phanben110/Robot-Omni-3-wheels-RTOS/3DSimulation/OMNI-cọc đồng/cọc đồng 6mm/M3 x 6mm A-F x 25mm Hexagon Male-Female Threaded Pillar.jpg

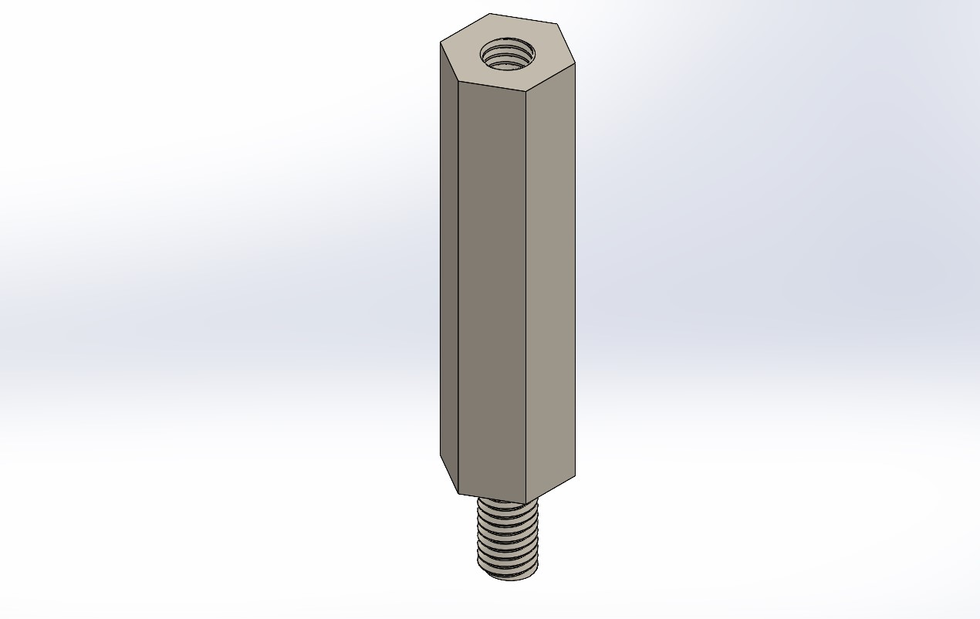
3DSimulation/OMNI-cọc đồng/cọc đồng 6mm/M3 x 6mm A-F x 25mm Hexagon Male-Female Threaded Pillar.jpg
