phanben110/Robot-Omni-3-wheels-RTOS/3DSimulation/OMNI-DRIVER/2016-12-01_19-26-19.png

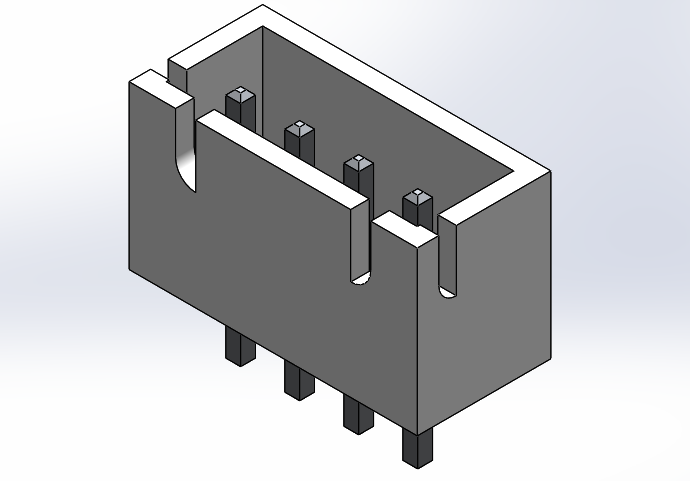
3DSimulation/OMNI-DRIVER/2016-12-01_19-26-19.png
