phanben110/Robot-Omni-3-wheels-RTOS/3DSimulation/OMNI-DRIVER/Cytron 30A Driver2.JPG

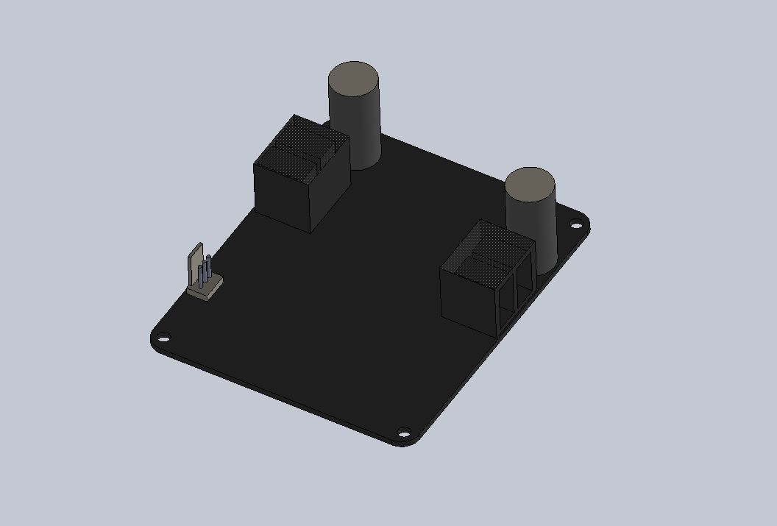
3DSimulation/OMNI-DRIVER/Cytron 30A Driver2.JPG
