phanben110/Robot-Omni-3-wheels-RTOS/3DSimulation/OMNI-DRIVER/Renderings/render.png

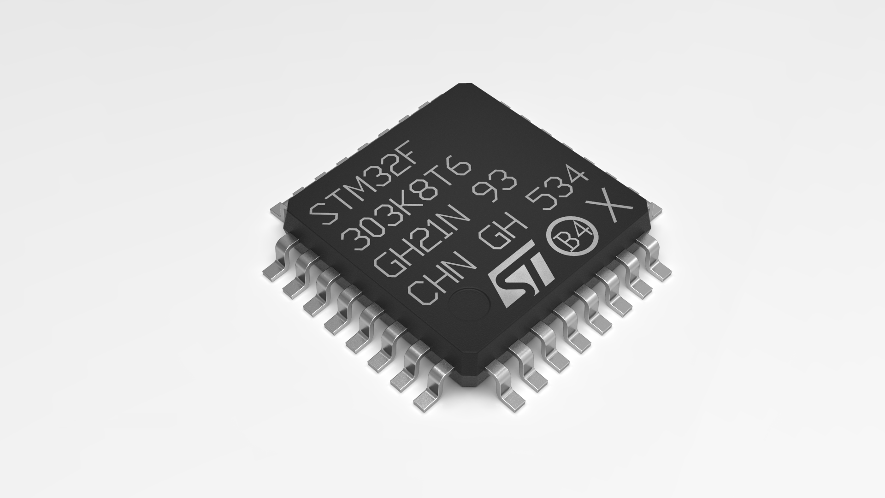
3DSimulation/OMNI-DRIVER/Renderings/render.png
