phanben110/Robot-Omni-3-wheels-RTOS/3DSimulation/OMNI-GÁ ĐỘNG CƠ/Screenshot (53).png

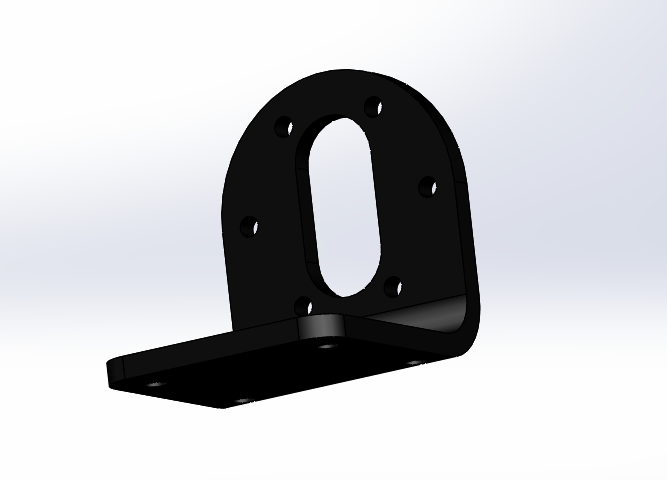
3DSimulation/OMNI-GÁ ĐỘNG CƠ/Screenshot (53).png
