phanben110/Robot-Omni-3-wheels-RTOS/3DSimulation/OMNI-ĐỘNG CƠ/JGB37-520.JPG

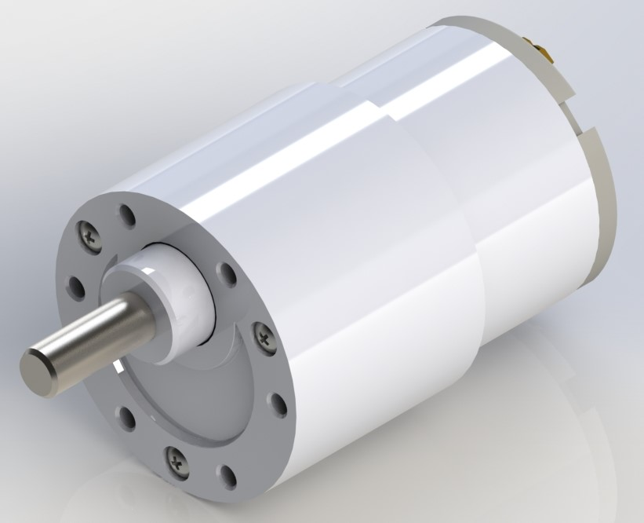
3DSimulation/OMNI-ĐỘNG CƠ/JGB37-520.JPG
