phanben110/Robot-Omni-3-wheels-RTOS/3DSimulation/OMNI-LIDAR/6.Lidar.SLDPRT

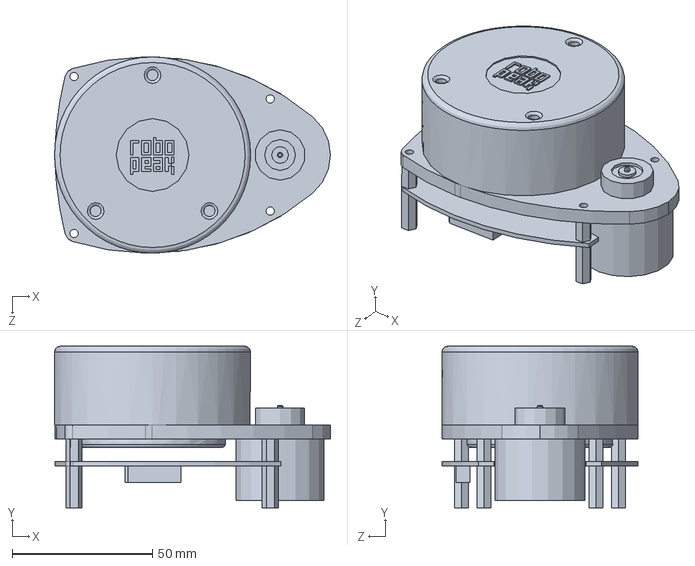
[picture p29: CAD file, 2022-06-20]
3DSimulation/OMNI-LIDAR/6.Lidar.SLDPRT
98.5 x 57.7 x 70.0 mm
