phanben110/Robot-Omni-3-wheels-RTOS/3DSimulation/OMNI-pin lipo/lipo-8-5-3cm.SLDPRT

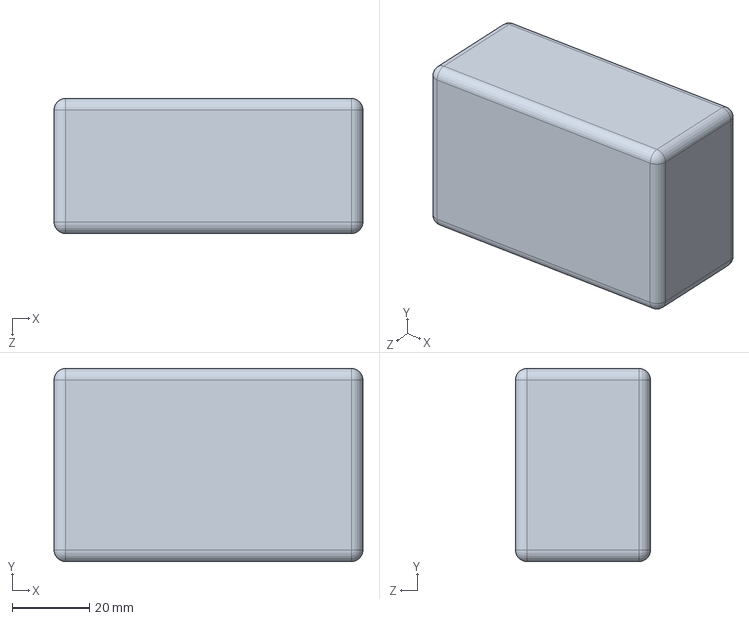
[picture p30: CAD file, 2022-06-20]
3DSimulation/OMNI-pin lipo/lipo-8-5-3cm.SLDPRT
80.0 x 50.0 x 35.0 mm
