phanben110/Robot-Omni-3-wheels-RTOS/3DSimulation/OMNI-raspberry 4/raspberry pi 4/Raspberry Pi 4 B.STEP

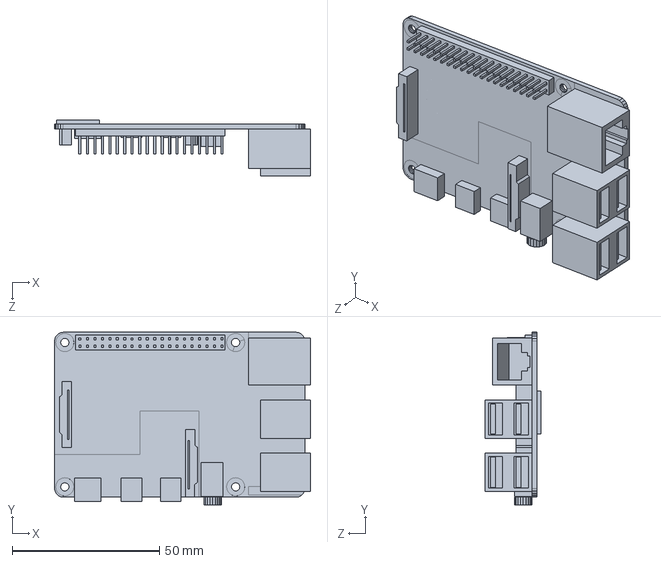
[picture p31: CAD file, 2022-06-20]
3DSimulation/OMNI-raspberry 4/raspberry pi 4/Raspberry Pi 4 B.STEP
86.9 x 58.6 x 19.0 mm
