phanben110/Robot-Omni-3-wheels-RTOS/3DSimulation/OMNI-ĐỘNG CƠ/diaencoder.SLDPRT

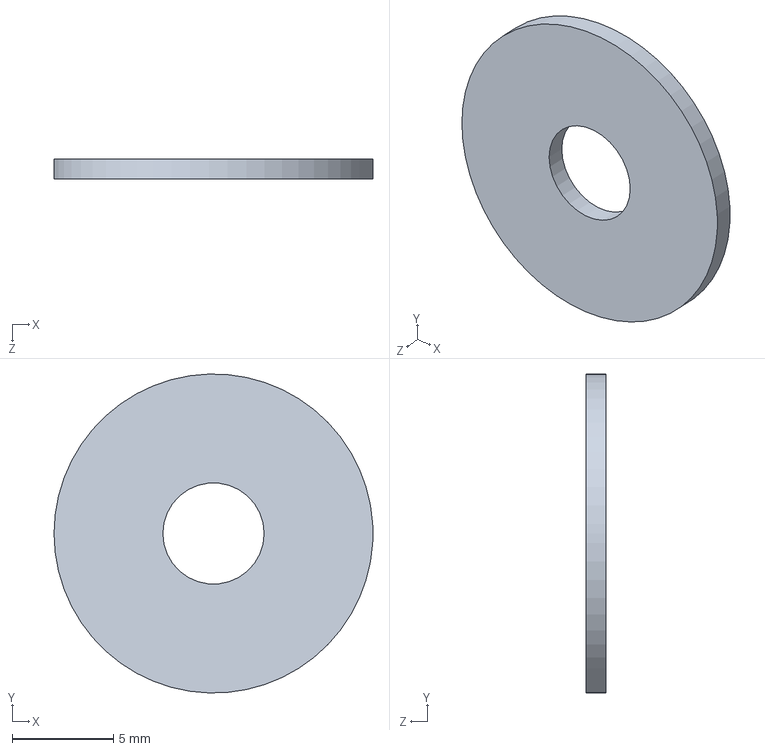
[picture p32: CAD file, 2022-06-20]
3DSimulation/OMNI-ĐỘNG CƠ/diaencoder.SLDPRT
15.8 x 15.7 x 1.00 mm
