phanben110/Robot-Omni-3-wheels-RTOS/3DSimulation/thành sân h=10cm.SLDPRT

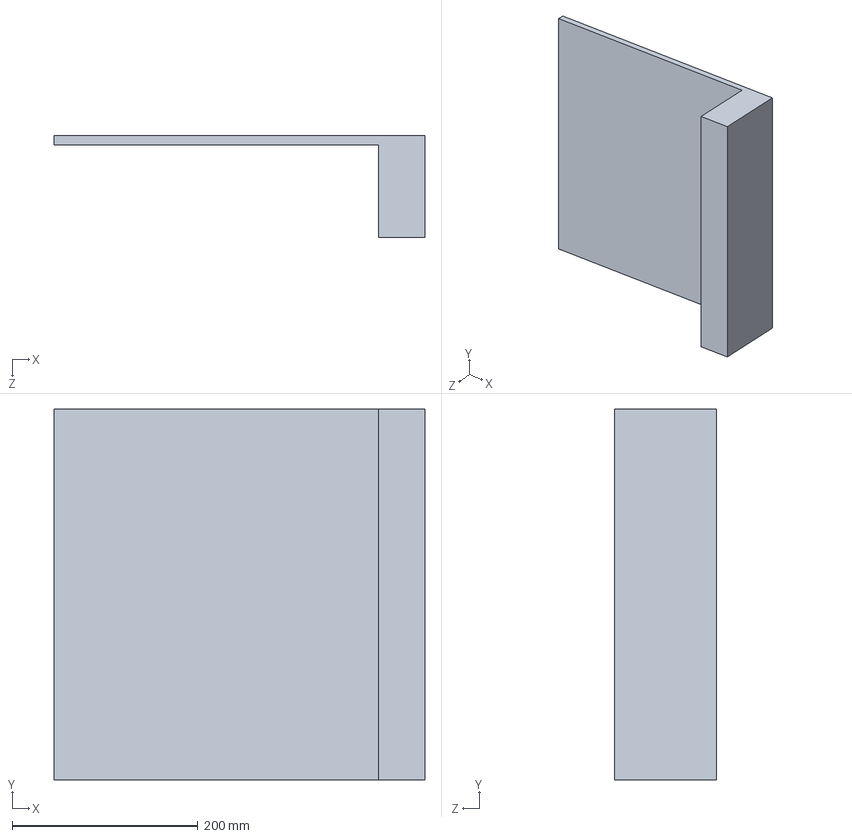
[picture p33: CAD file, 2022-06-20]
3DSimulation/thành sân h=10cm.SLDPRT
400.0 x 400.0 x 110.0 mm
