phanben110/Robot-Omni-3-wheels-RTOS/3DSimulation/file cắt cnc/VERSION 2.95 (main)/khung robot ver 2.95 mat duoi inox 3li.DXF

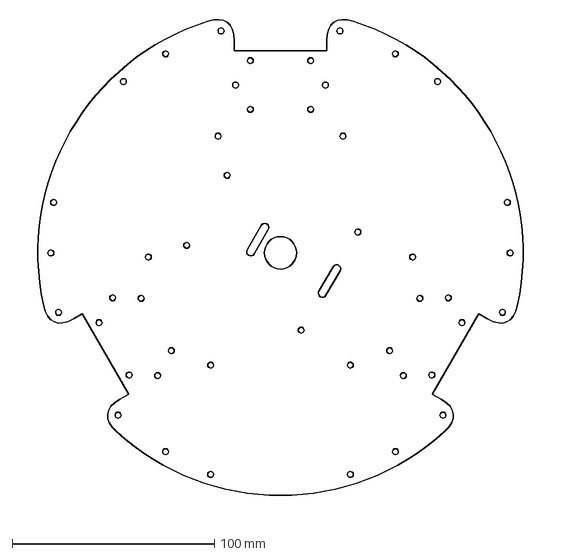
[picture p34: CAD file, 2022-06-20]
3DSimulation/file cắt cnc/VERSION 2.95 (main)/khung robot ver 2.95 mat duoi inox 3li.DXF
261.5 x 247.6 mm
