phanben110/Robot-Omni-3-wheels-RTOS/3DSimulation/file cắt cnc/VERSION 3.2/khung robot ver 3.2 mat duoi.DXF

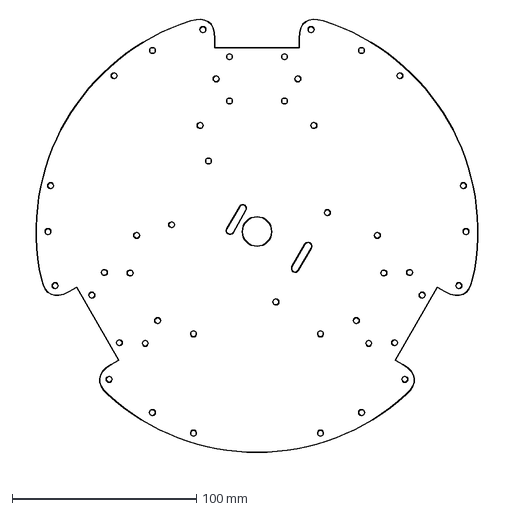
[picture p35: CAD file, 2022-06-20]
3DSimulation/file cắt cnc/VERSION 3.2/khung robot ver 3.2 mat duoi.DXF
261.5 x 247.6 mm
