phanben110/Robot-Omni-3-wheels-RTOS/3DSimulation/OMNI-BÁNH NHÔM 60mm/Wheel/Wheel - Rubber-8.STL

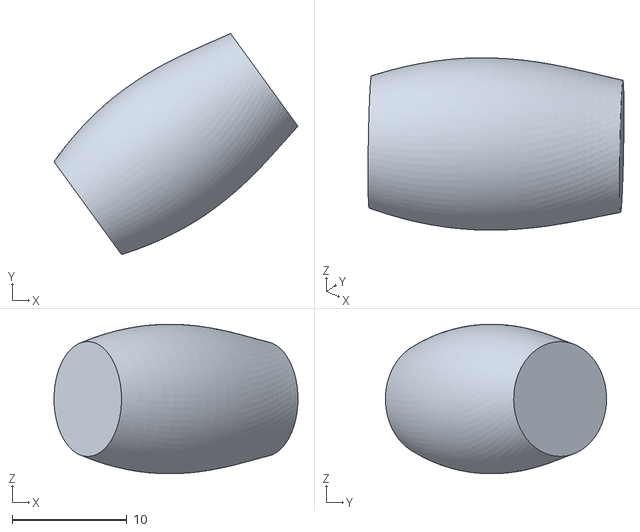
[picture p36: CAD file, 2022-06-20]
3DSimulation/OMNI-BÁNH NHÔM 60mm/Wheel/Wheel - Rubber-8.STL
21.2 x 19.3 x 13.0
