phanben110/Robot-Omni-3-wheels-RTOS/3DSimulation/OMNI-DRIVER/ırlz44nstep.STEP

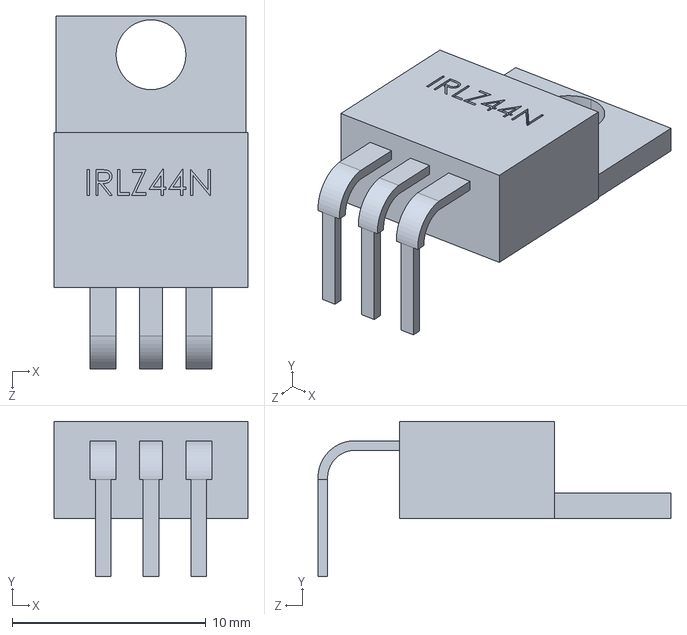
[picture p37: CAD file, 2022-06-20]
3DSimulation/OMNI-DRIVER/ırlz44nstep.STEP
10.0 x 8.00 x 18.2 mm
