phanben110/Robot-Omni-3-wheels-RTOS/3DSimulation/OMNI-encoder/38 mm OD, 6 mm Shaft, Incremental Optical Rotary Encoder.STEP

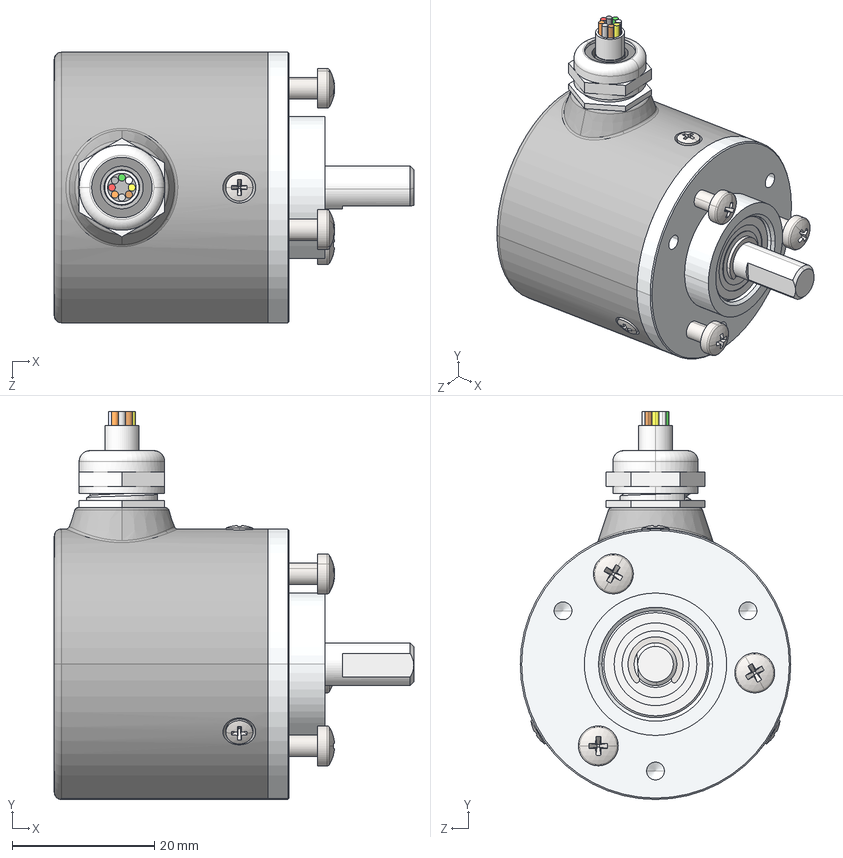
[picture p38: CAD file, 2022-06-20]
3DSimulation/OMNI-encoder/38 mm OD, 6 mm Shaft, Incremental Optical Rotary Encoder.STEP
50.5 x 54.5 x 38.0 mm
Encasing, 38 mm OD, 6 mm Shaft, Incremental Optical Rotary Encoder
Shaft Holding Body, 38 mm OD, 6 mm Shaft, Incremental Optical Rotary Encoder
696Z Ball Bearing, 38 mm OD, 6 mm Shaft, Incremental Optical Rotary Encoder_default
Shaft, 38 mm OD, 6 mm Shaft, Incremental Optical Rotary Encoder
Grommet, 38 mm OD, 6 mm Shaft, Incremental Optical Rotary Encoder
Cable Gland Coupling Nut, 38 mm OD, 6 mm Shaft, Incremental Optical Rotary Encoder
Cable Gland Coupling Fastening Nut, 38 mm OD, 6 mm Shaft, Incremental Optical Rotary Encoder
Cable, 38 mm OD, 6 mm Shaft, Incremental Optical Rotary Encoder
oval head_am_B18.6.7M - M2 x 0.4 x 4 Type I Cross Recessed OHMS --4N x 3
c-ring external retaining ring_am_B27.8M - 3FM1-6
pan cross head_am_B18.6.7M - M3 x 0.5 x 8 Type I Cross Recessed PHMS --8N x 3
