phanben110/Robot-Omni-3-wheels-RTOS/3DSimulation/OMNI-KHUNG ROBOT/thanh bắt chéo cố định 2 chân động cơ.SLDPRT

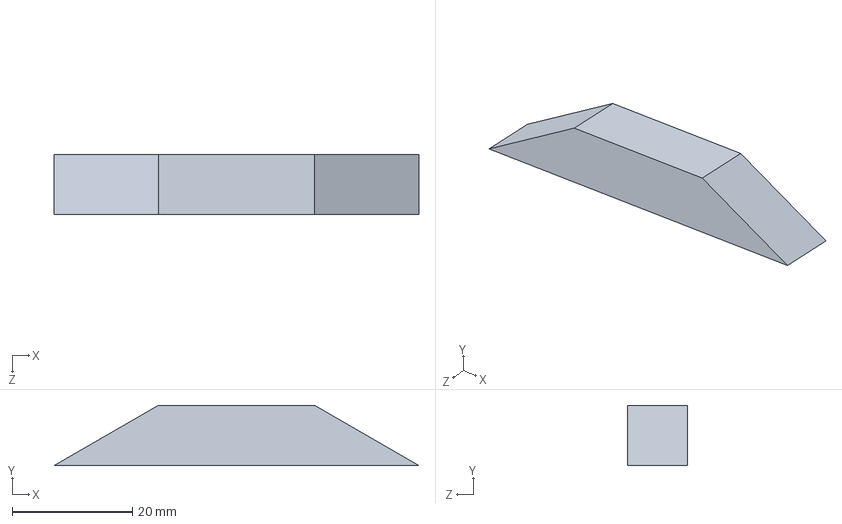
[picture p39: CAD file, 2022-06-20]
3DSimulation/OMNI-KHUNG ROBOT/thanh bắt chéo cố định 2 chân động cơ.SLDPRT
60.6 x 10.0 x 10.0 mm
