phanben110/Robot-Omni-3-wheels-RTOS/3DSimulation/OMNI-ĐỘNG CƠ/GEARED BODY, MOTOR, JGB37-520.SLDPRT

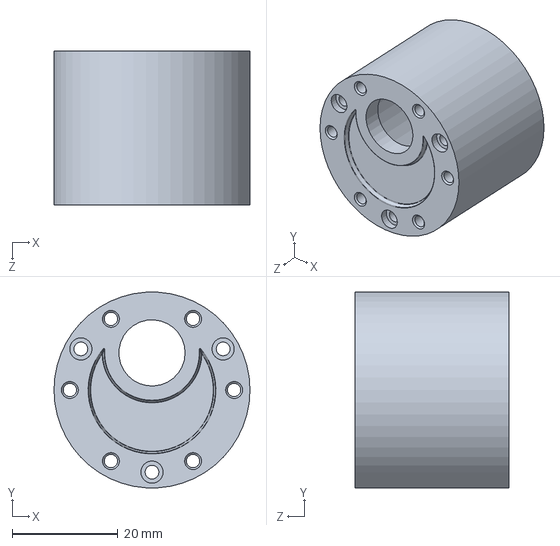
[picture p40: CAD file, 2022-06-20]
3DSimulation/OMNI-ĐỘNG CƠ/GEARED BODY, MOTOR, JGB37-520.SLDPRT
37.0 x 36.9 x 29.0 mm
