phanben110/Robot-Omni-3-wheels-RTOS/3DSimulation/OMNI-BÁNH NHÔM 60mm/Wheel/Wheel - Rubber-10.STL

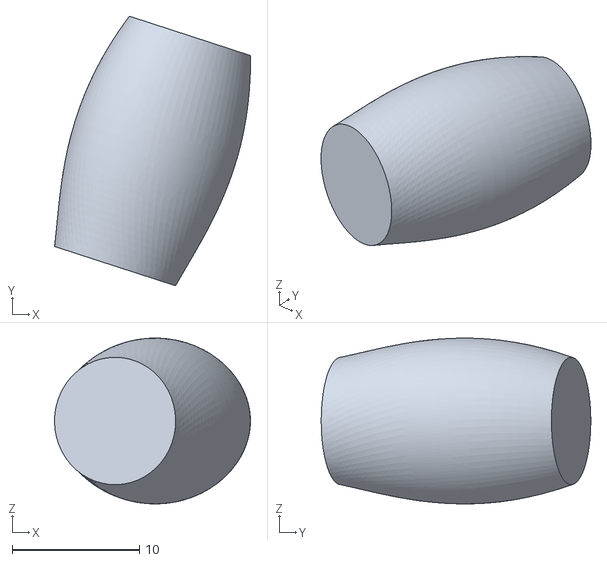
[picture p41: CAD file, 2022-06-20]
3DSimulation/OMNI-BÁNH NHÔM 60mm/Wheel/Wheel - Rubber-10.STL
15.4 x 21.2 x 13.0
