phanben110/Robot-Omni-3-wheels-RTOS/3DSimulation/OMNI-KHUNG ROBOT/file test M3.SLDPRT

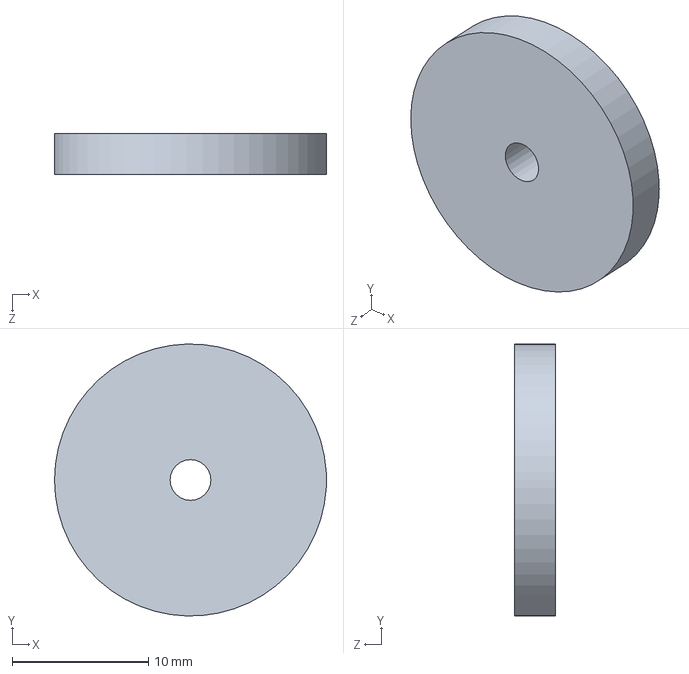
[picture p43: CAD file, 2022-06-20]
3DSimulation/OMNI-KHUNG ROBOT/file test M3.SLDPRT
20.0 x 20.0 x 3.00 mm
