phanben110/Robot-Omni-3-wheels-RTOS/3DSimulation/OMNI-ĐỘNG CƠ/PLASTIC COVER, DC MOTOR, JGB37-520.SLDPRT

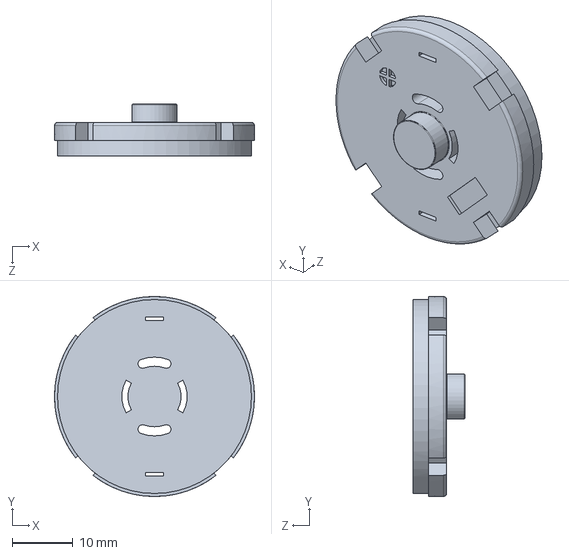
[picture p44: CAD file, 2022-06-20]
3DSimulation/OMNI-ĐỘNG CƠ/PLASTIC COVER, DC MOTOR, JGB37-520.SLDPRT
33.0 x 33.0 x 8.50 mm
