phanben110/Robot-Omni-3-wheels-RTOS/3DSimulation/OMNI-encoder/Shaft, 38 mm OD, 6 mm Shaft, Incremental Optical Rotary Encoder.SLDPRT

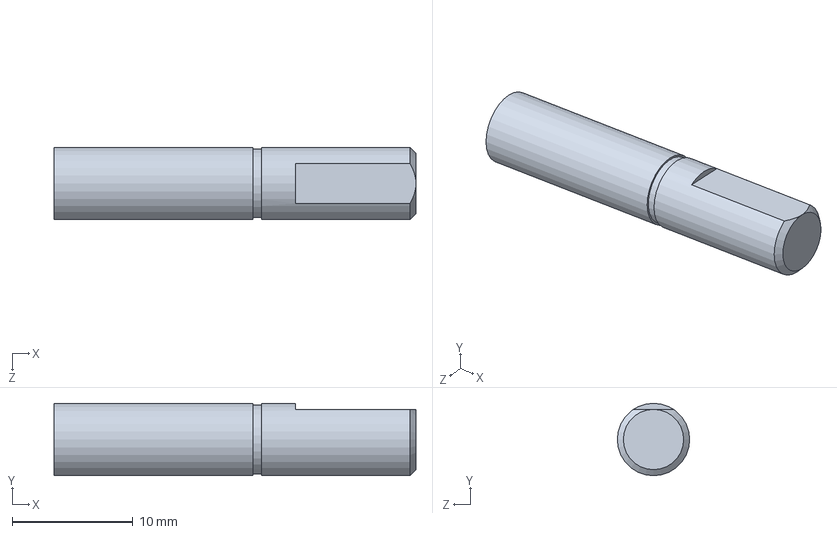
[picture p45: CAD file, 2022-06-20]
3DSimulation/OMNI-encoder/Shaft, 38 mm OD, 6 mm Shaft, Incremental Optical Rotary Encoder.SLDPRT
30.0 x 6.00 x 6.00 mm
