phanben110/Robot-Omni-3-wheels-RTOS/3DSimulation/OMNI-KHUNG ROBOT/khung chân của 1 động cơ.SLDPRT

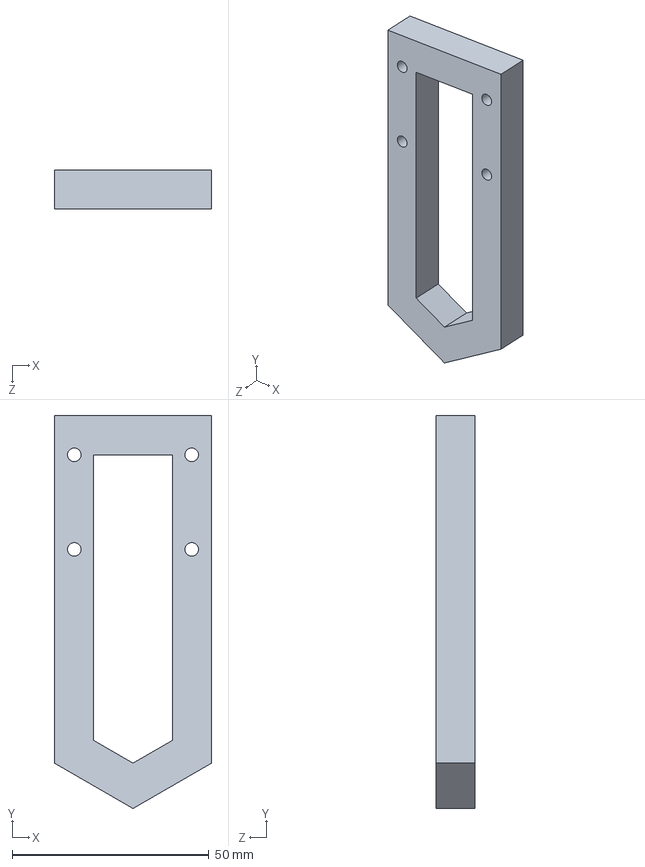
[picture p46: CAD file, 2022-06-20]
3DSimulation/OMNI-KHUNG ROBOT/khung chân của 1 động cơ.SLDPRT
40.0 x 100.0 x 10.0 mm
