phanben110/Robot-Omni-3-wheels-RTOS/3DSimulation/OMNI-ĐỘNG CƠ/COUPLING BRACKET, GEARED BODY TO DC MOTOR, JGB37-520.SLDPRT

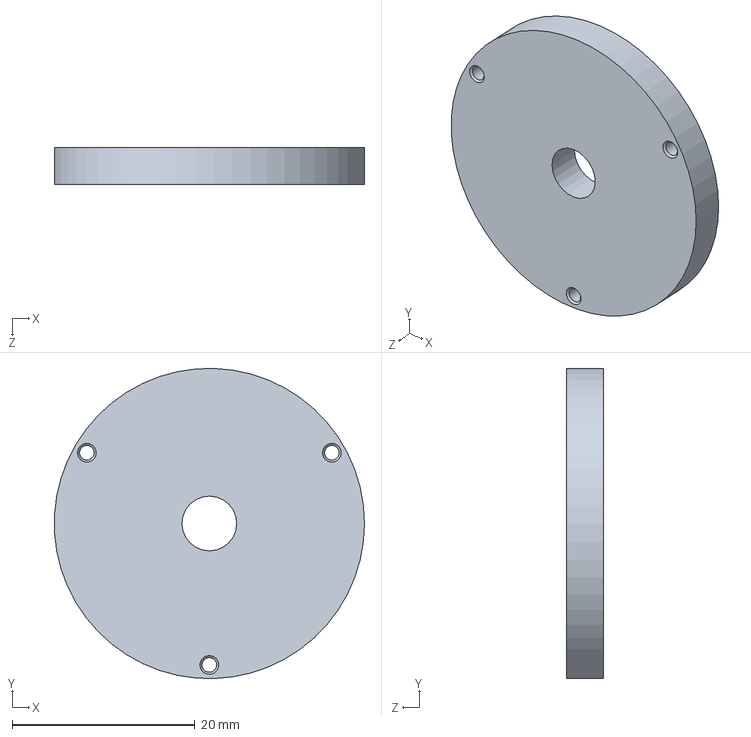
[picture p47: CAD file, 2022-06-20]
3DSimulation/OMNI-ĐỘNG CƠ/COUPLING BRACKET, GEARED BODY TO DC MOTOR, JGB37-520.SLDPRT
34.0 x 34.0 x 4.00 mm
