phanben110/Robot-Omni-3-wheels-RTOS/3DSimulation/OMNI-DRIVER/board driver.SLDPRT

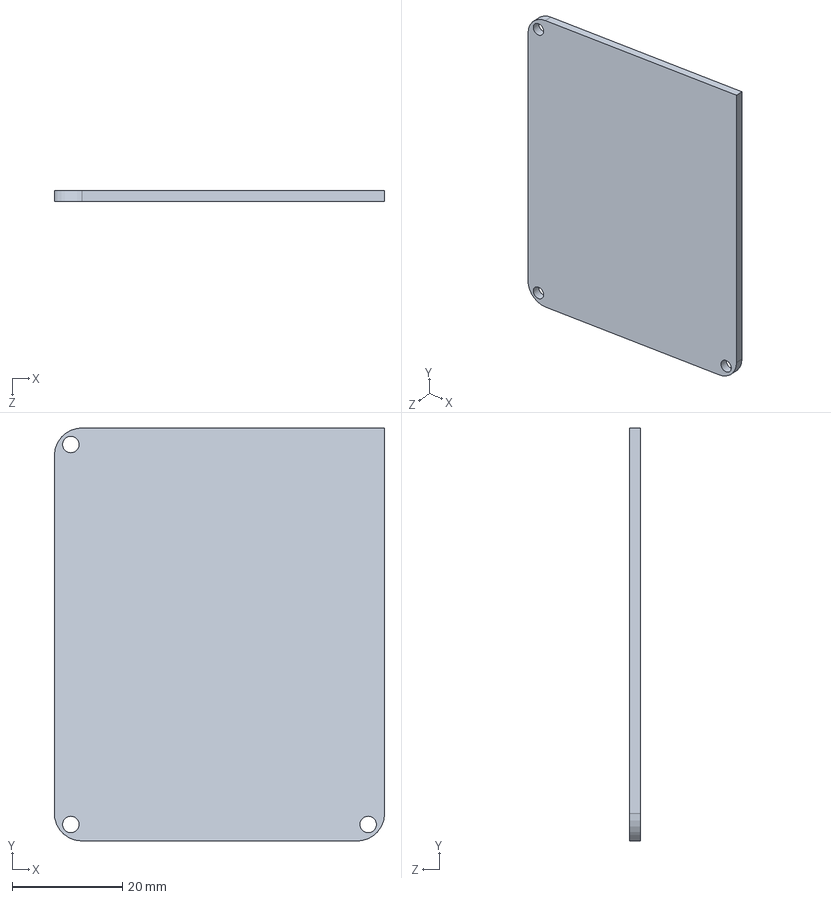
[picture p48: CAD file, 2022-06-20]
3DSimulation/OMNI-DRIVER/board driver.SLDPRT
60.0 x 75.0 x 2.00 mm
