phanben110/Robot-Omni-3-wheels-RTOS/3DSimulation/OMNI-encoder/Cable, 38 mm OD, 6 mm Shaft, Incremental Optical Rotary Encoder.SLDPRT

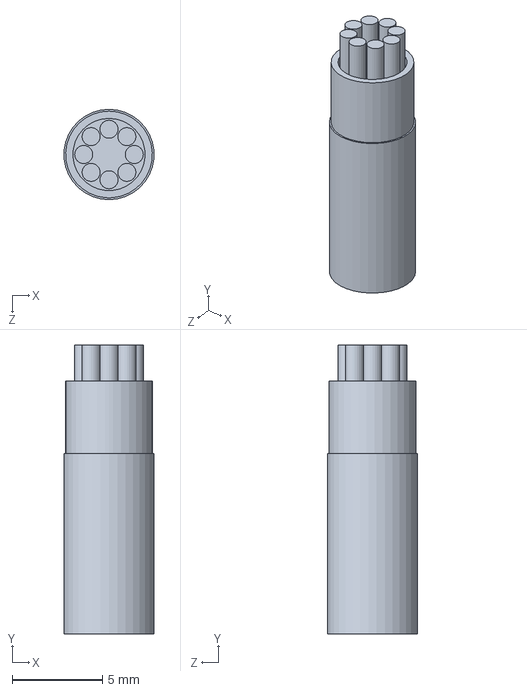
[picture p49: CAD file, 2022-06-20]
3DSimulation/OMNI-encoder/Cable, 38 mm OD, 6 mm Shaft, Incremental Optical Rotary Encoder.SLDPRT
4.98 x 16.0 x 5.00 mm
