phanben110/Robot-Omni-3-wheels-RTOS/3DSimulation/OMNI-KHUNG ROBOT/khung robot cnc.SLDPRT

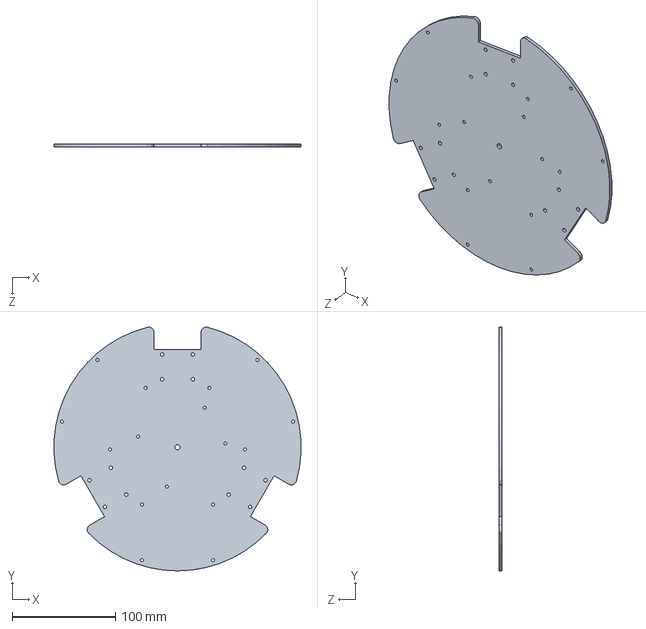
[picture p50: CAD file, 2022-06-20]
3DSimulation/OMNI-KHUNG ROBOT/khung robot cnc.SLDPRT
239.7 x 236.6 x 3.00 mm
