phanben110/Robot-Omni-3-wheels-RTOS/3DSimulation/OMNI-ĐỘNG CƠ/DC MOTOR, JGB37-520.SLDPRT

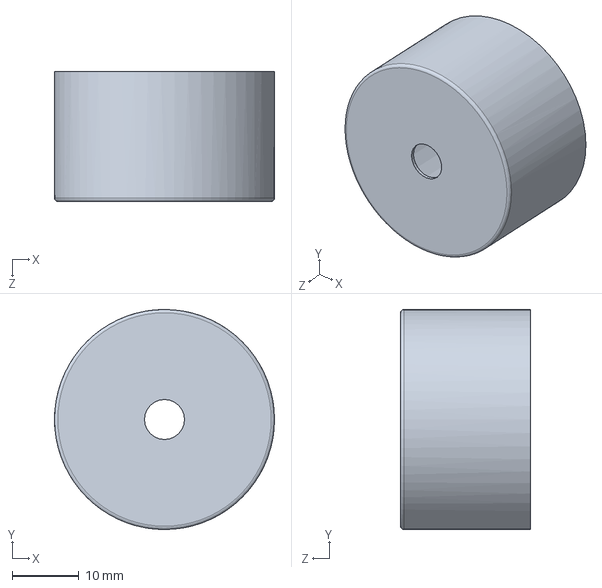
[picture p51: CAD file, 2022-06-20]
3DSimulation/OMNI-ĐỘNG CƠ/DC MOTOR, JGB37-520.SLDPRT
33.0 x 33.0 x 19.5 mm
