phanben110/Robot-Omni-3-wheels-RTOS/3DSimulation/OMNI-BÁNH NHÔM 60mm/Wheel/Wheel - Alu_Base-1.STL

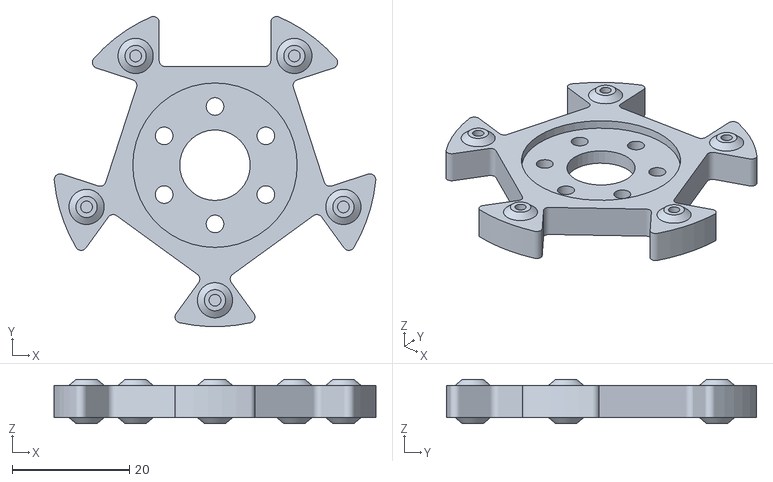
[picture p52: CAD file, 2022-06-20]
3DSimulation/OMNI-BÁNH NHÔM 60mm/Wheel/Wheel - Alu_Base-1.STL
54.8 x 52.8 x 7.50
