phanben110/Robot-Omni-3-wheels-RTOS/3DSimulation/OMNI-encoder/Cable Gland Coupling Fastening Nut, 38 mm OD, 6 mm Shaft, Incremental Optical Rotary Encoder.SLDPRT

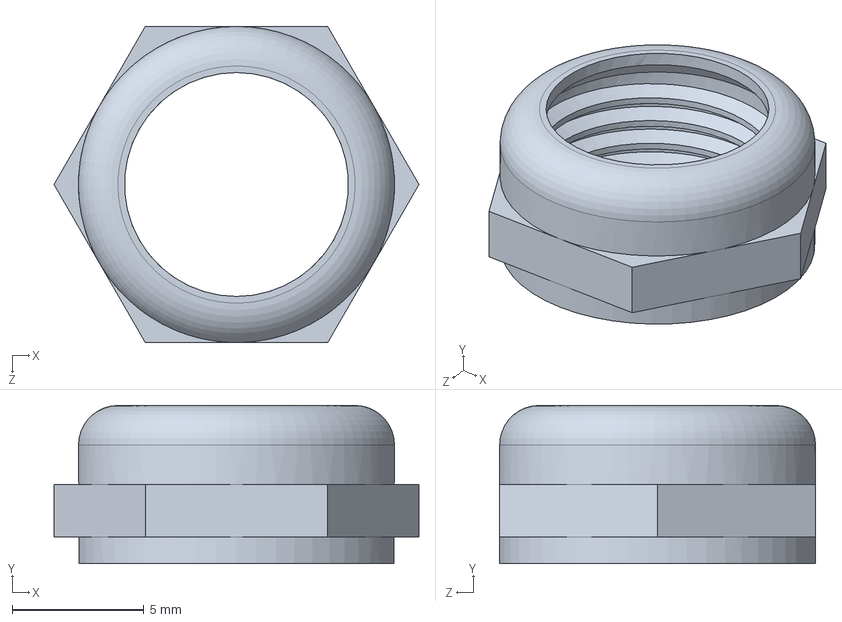
[picture p53: CAD file, 2022-06-20]
3DSimulation/OMNI-encoder/Cable Gland Coupling Fastening Nut, 38 mm OD, 6 mm Shaft, Incremental Optical Rotary Encoder.SLDPRT
13.9 x 6.00 x 12.0 mm
