phanben110/Robot-Omni-3-wheels-RTOS/3DSimulation/OMNI-KHUNG ROBOT/khung robot ver2 mat tren co the chinh sua.SLDPRT

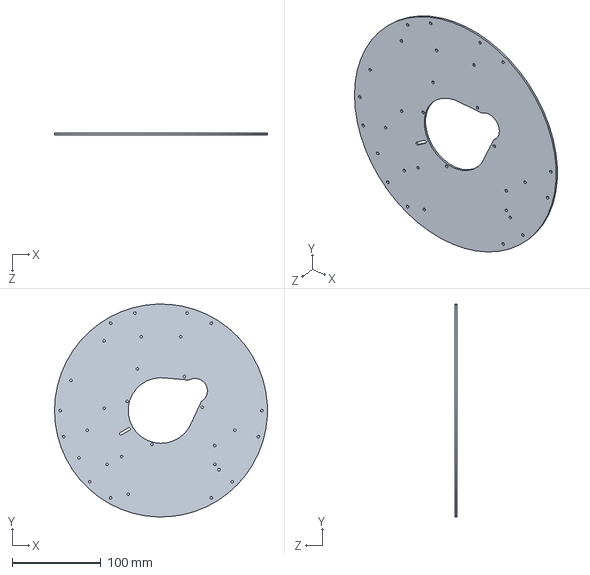
[picture p54: CAD file, 2022-06-20]
3DSimulation/OMNI-KHUNG ROBOT/khung robot ver2 mat tren co the chinh sua.SLDPRT
240.0 x 239.9 x 2.00 mm
