phanben110/Robot-Omni-3-wheels-RTOS/3DSimulation/OMNI-ĐỘNG CƠ/SHAFT COUPLER, JGB37-520.SLDPRT

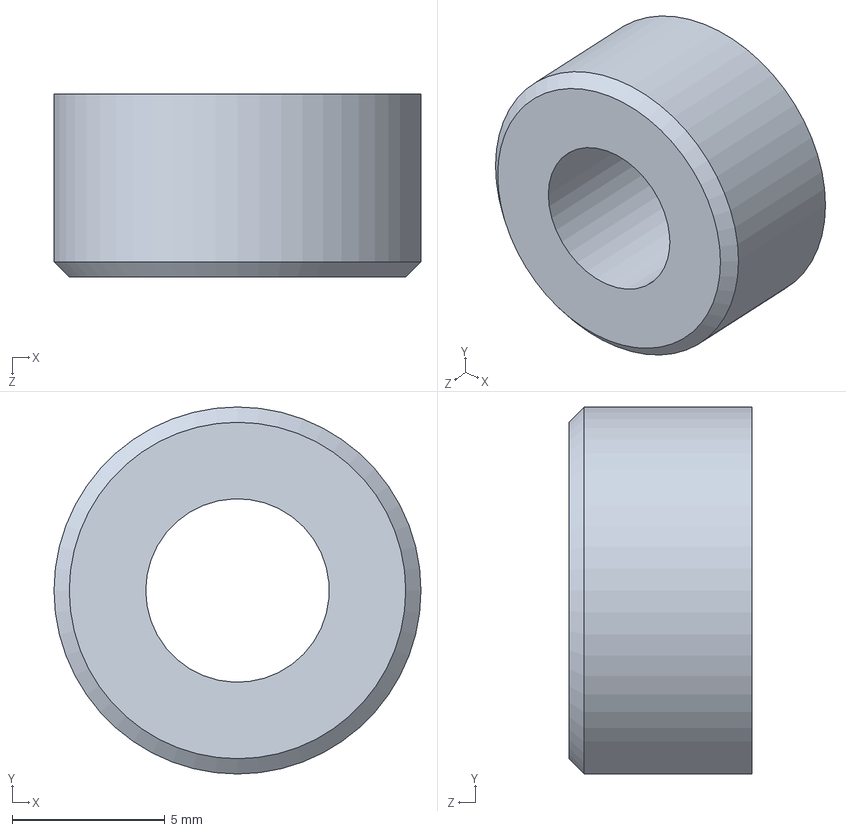
[picture p55: CAD file, 2022-06-20]
3DSimulation/OMNI-ĐỘNG CƠ/SHAFT COUPLER, JGB37-520.SLDPRT
12.0 x 12.0 x 6.00 mm
