phanben110/Robot-Omni-3-wheels-RTOS/3DSimulation/OMNI-encoder/Shaft Holding Body, 38 mm OD, 6 mm Shaft, Incremental Optical Rotary Encoder.SLDPRT

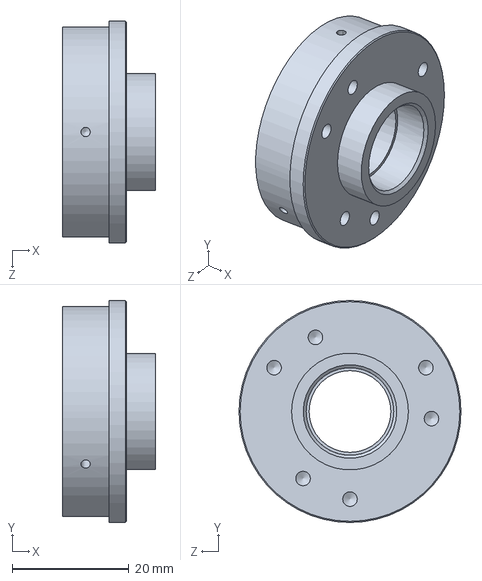
[picture p56: CAD file, 2022-06-20]
3DSimulation/OMNI-encoder/Shaft Holding Body, 38 mm OD, 6 mm Shaft, Incremental Optical Rotary Encoder.SLDPRT
16.0 x 38.0 x 38.0 mm
