phanben110/Robot-Omni-3-wheels-RTOS/3DSimulation/OMNI-KHUNG ROBOT/khung robot cnc mặt trên.SLDPRT

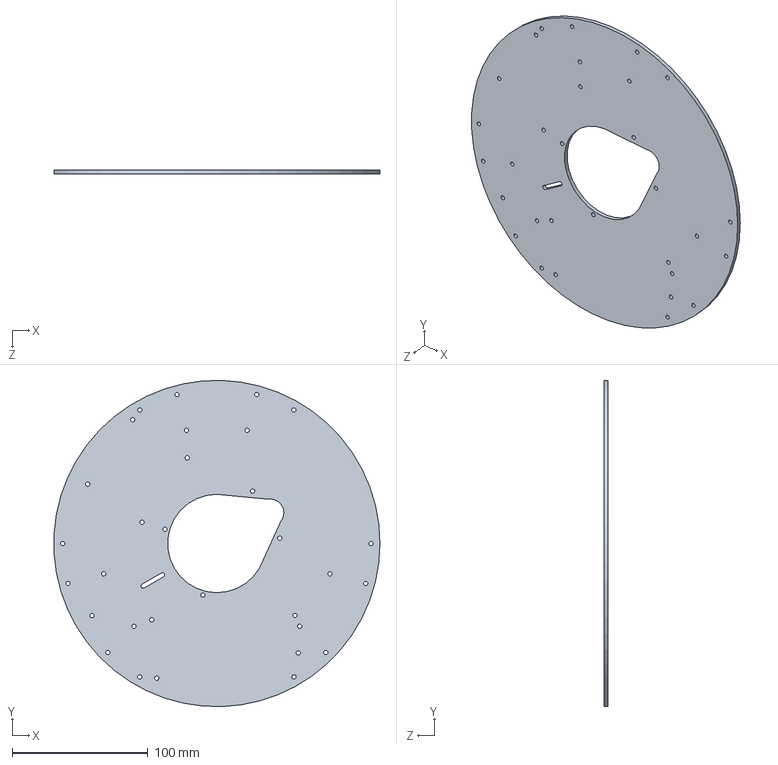
[picture p57: CAD file, 2022-06-20]
3DSimulation/OMNI-KHUNG ROBOT/khung robot cnc mặt trên.SLDPRT
240.3 x 240.4 x 3.00 mm
