phanben110/Robot-Omni-3-wheels-RTOS/3DSimulation/OMNI-ĐỘNG CƠ/JGB37-520.STEP

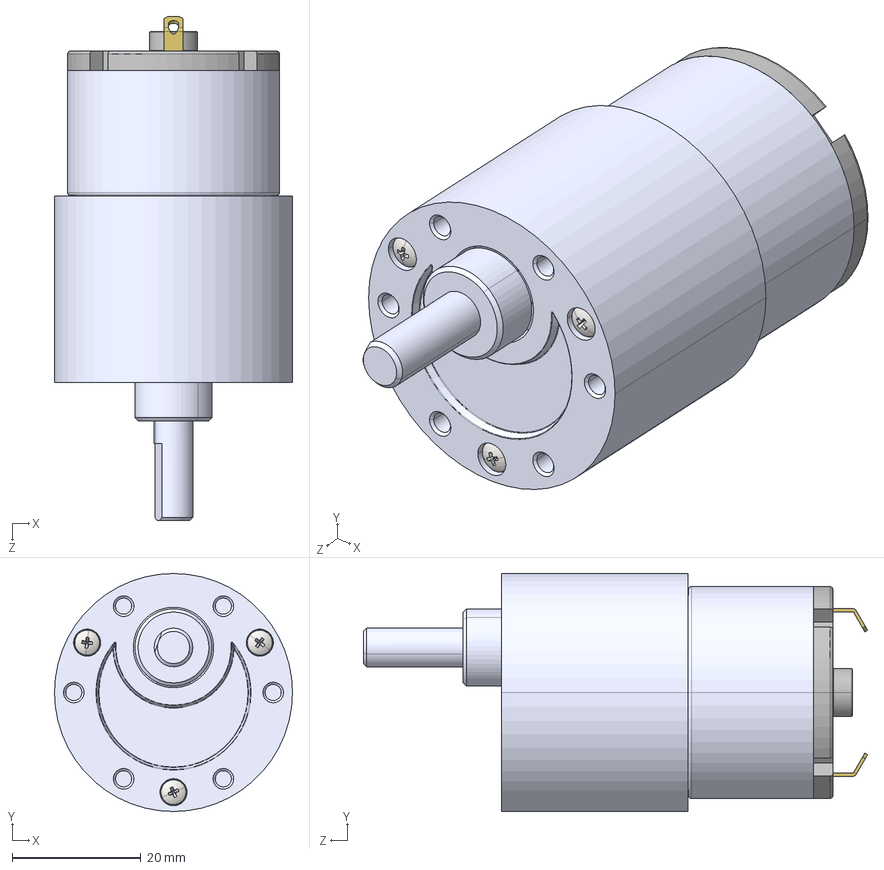
[picture p58: CAD file, 2022-06-20]
3DSimulation/OMNI-ĐỘNG CƠ/JGB37-520.STEP
37.0 x 37.0 x 78.4 mm
GEARED BODY, MOTOR, JGB37-520
DC MOTOR, JGB37-520
MOTOR SHAFT, JGB37-520
SHAFT COUPLER, JGB37-520
COUPLING BRACKET, GEARED BODY TO DC MOTOR, JGB37-520
PLASTIC COVER, DC MOTOR, JGB37-520
CONNECTION, DC MOTOR, JGB37-520 x 2
pan cross head_am_B18.6.7M - M2 x 0.4 x 25 Type I Cross Recessed PHMS --25N x 3
