phanben110/Robot-Omni-3-wheels-RTOS/3DSimulation/OMNI-DRIVER/5x15 Fuse with holder.STEP

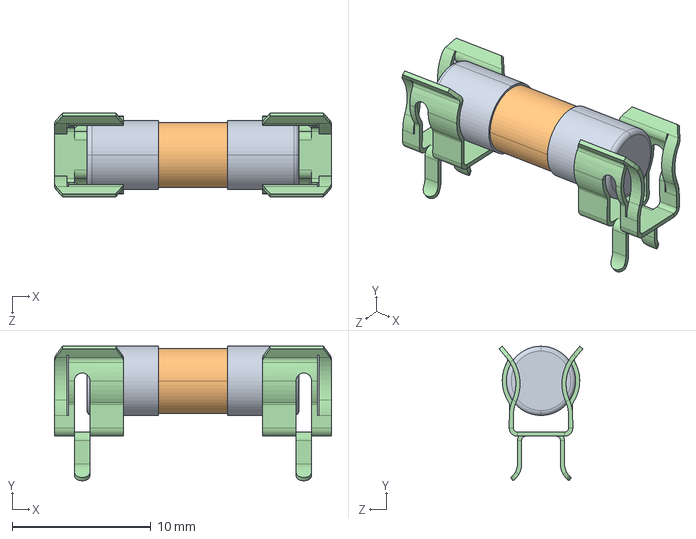
[picture p59: CAD file, 2022-06-20]
3DSimulation/OMNI-DRIVER/5x15 Fuse with holder.STEP
20.0 x 9.72 x 6.06 mm
