phanben110/Robot-Omni-3-wheels-RTOS/3DSimulation/OMNI-encoder/Grommet, 38 mm OD, 6 mm Shaft, Incremental Optical Rotary Encoder.SLDPRT

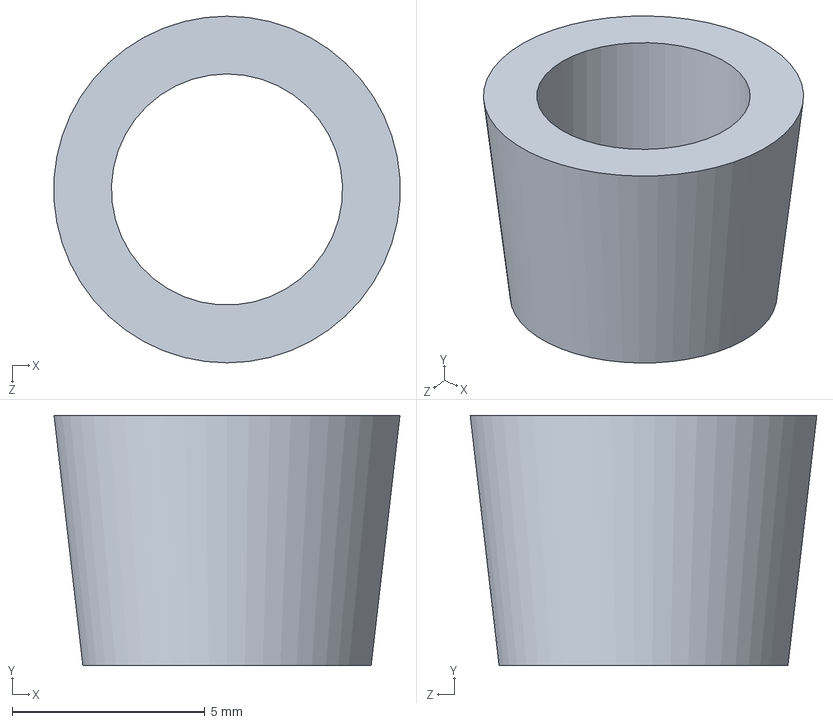
[picture p60: CAD file, 2022-06-20]
3DSimulation/OMNI-encoder/Grommet, 38 mm OD, 6 mm Shaft, Incremental Optical Rotary Encoder.SLDPRT
8.98 x 6.50 x 9.00 mm
