phanben110/Robot-Omni-3-wheels-RTOS/3DSimulation/OMNI-ĐỘNG CƠ/MOTOR SHAFT, JGB37-520.SLDPRT

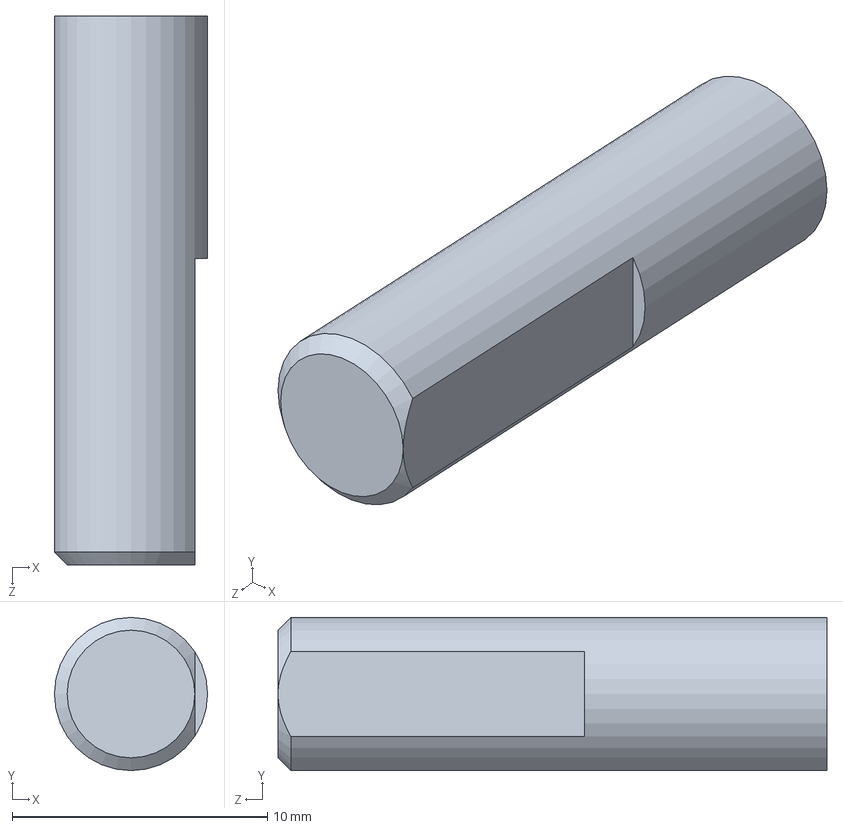
[picture p61: CAD file, 2022-06-20]
3DSimulation/OMNI-ĐỘNG CƠ/MOTOR SHAFT, JGB37-520.SLDPRT
6.00 x 6.00 x 21.5 mm
