phanben110/Robot-Omni-3-wheels-RTOS/3DSimulation/OMNI-DRIVER/Cytron 30A Driver.SLDPRT

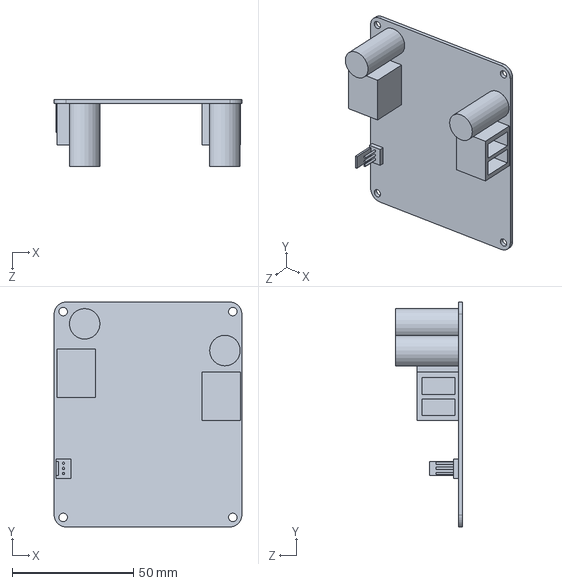
[picture p62: CAD file, 2022-06-20]
3DSimulation/OMNI-DRIVER/Cytron 30A Driver.SLDPRT
77.4 x 92.7 x 27.7 mm
