phanben110/Robot-Omni-3-wheels-RTOS/3DSimulation/OMNI-encoder/696Z Ball Bearing, 38 mm OD, 6 mm Shaft, Incremental Optical Rotary Encoder.SLDPRT

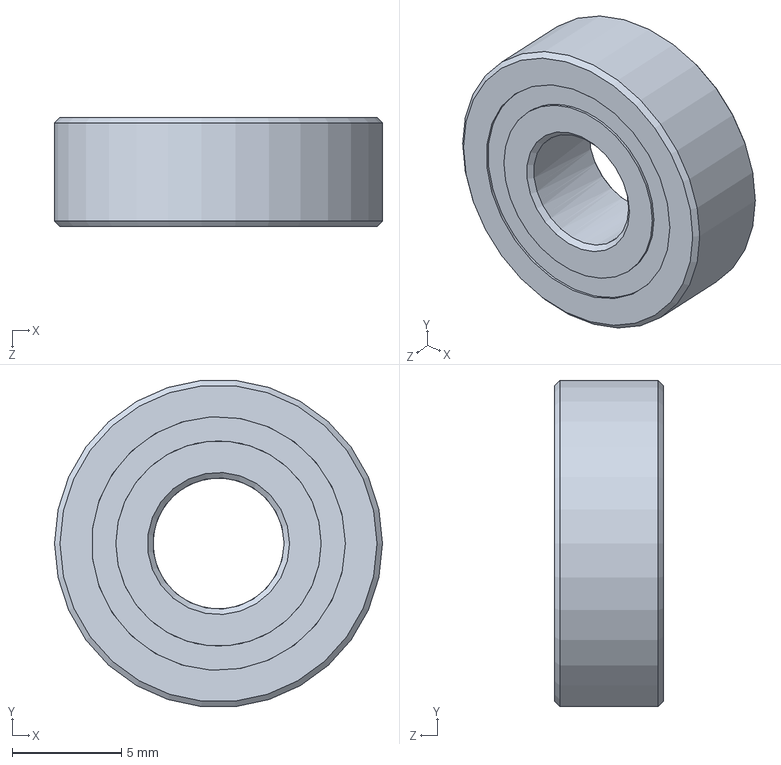
[picture p63: CAD file, 2022-06-20]
3DSimulation/OMNI-encoder/696Z Ball Bearing, 38 mm OD, 6 mm Shaft, Incremental Optical Rotary Encoder.SLDPRT
15.0 x 14.9 x 5.00 mm
