phanben110/Robot-Omni-3-wheels-RTOS/3DSimulation/OMNI-ĐỘNG CƠ/CONNECTION, DC MOTOR, JGB37-520.SLDPRT

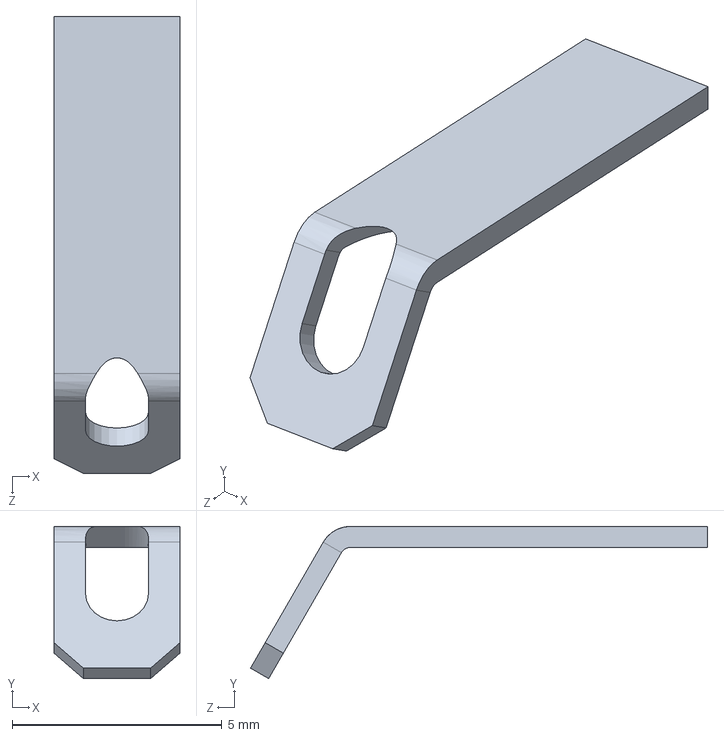
[picture p64: CAD file, 2022-06-20]
3DSimulation/OMNI-ĐỘNG CƠ/CONNECTION, DC MOTOR, JGB37-520.SLDPRT
3.00 x 3.62 x 10.9 mm
