phanben110/Robot-Omni-3-wheels-RTOS/3DSimulation/OMNI-DRIVER/IL-G-2P-S3T2-SA.STEP

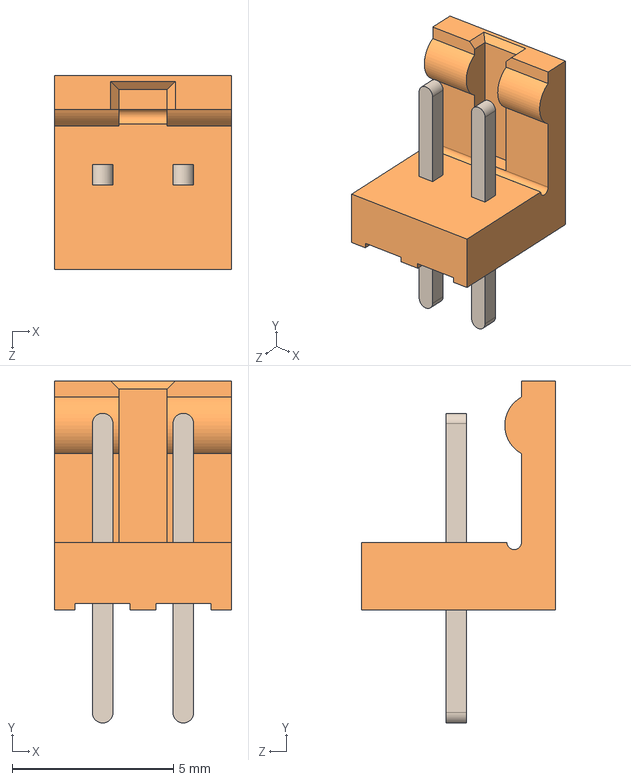
[picture p65: CAD file, 2022-06-20]
3DSimulation/OMNI-DRIVER/IL-G-2P-S3T2-SA.STEP
5.50 x 10.6 x 6.00 mm
