phanben110/Robot-Omni-3-wheels-RTOS/3DSimulation/OMNI-BÁNH NHÔM 60mm/Wheel/Wheel - Middle_Plastic-1.STL

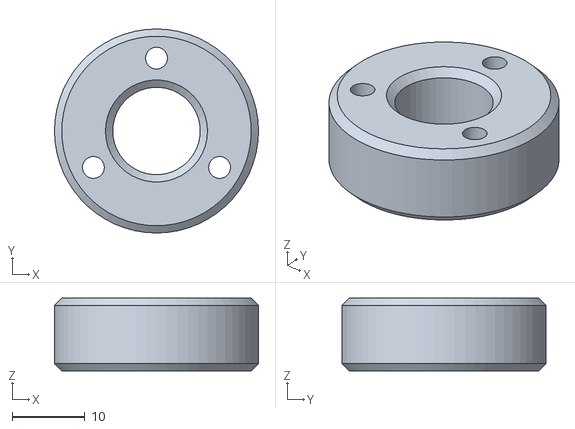
[picture p66: CAD file, 2022-06-20]
3DSimulation/OMNI-BÁNH NHÔM 60mm/Wheel/Wheel - Middle_Plastic-1.STL
28.0 x 28.0 x 10.00
